jpwolfe9912/F051-ESC-4in1-V1/PNGs/3D_Back.png

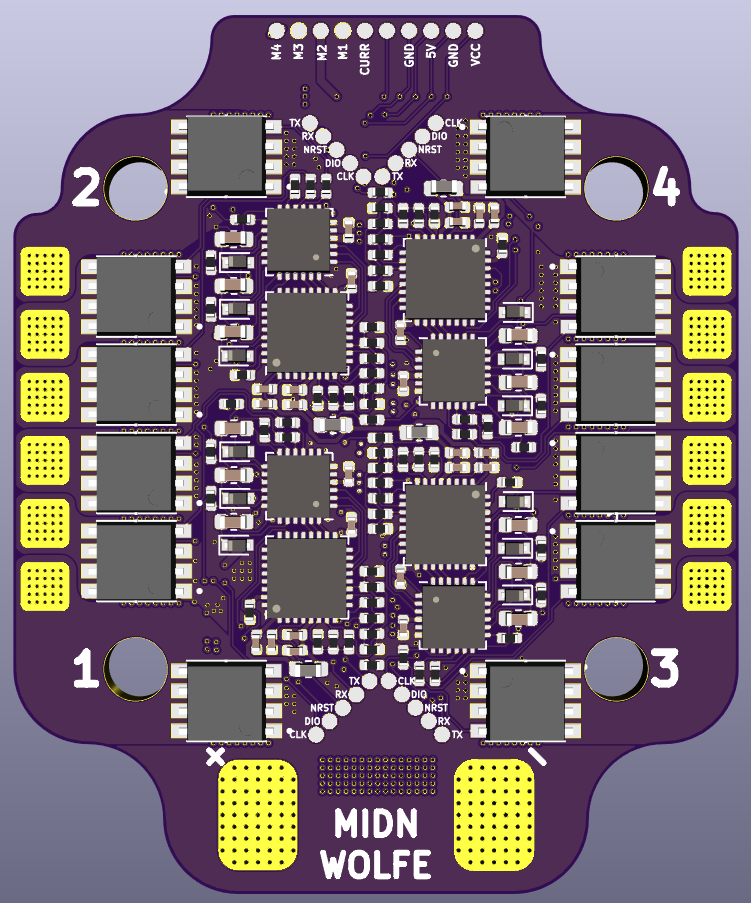
PNGs/3D_Back.png
