jpwolfe9912/F051-ESC-4in1-V1/PNGs/Design_In1Fill.png

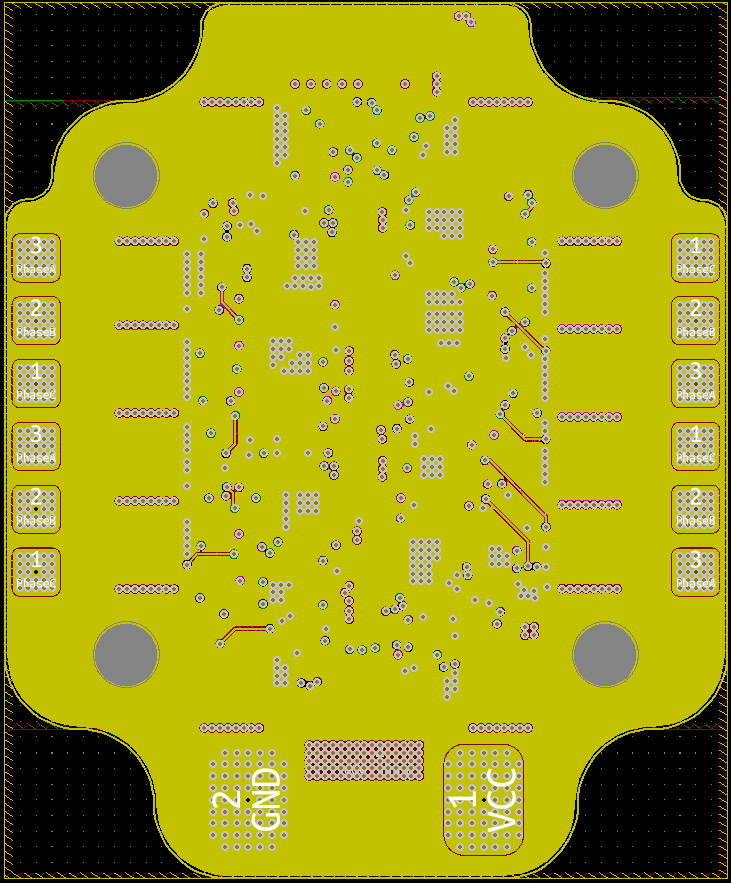
PNGs/Design_In1Fill.png
