jpwolfe9912/F051-ESC-4in1-V1/PNGs/Schematic_Main.png

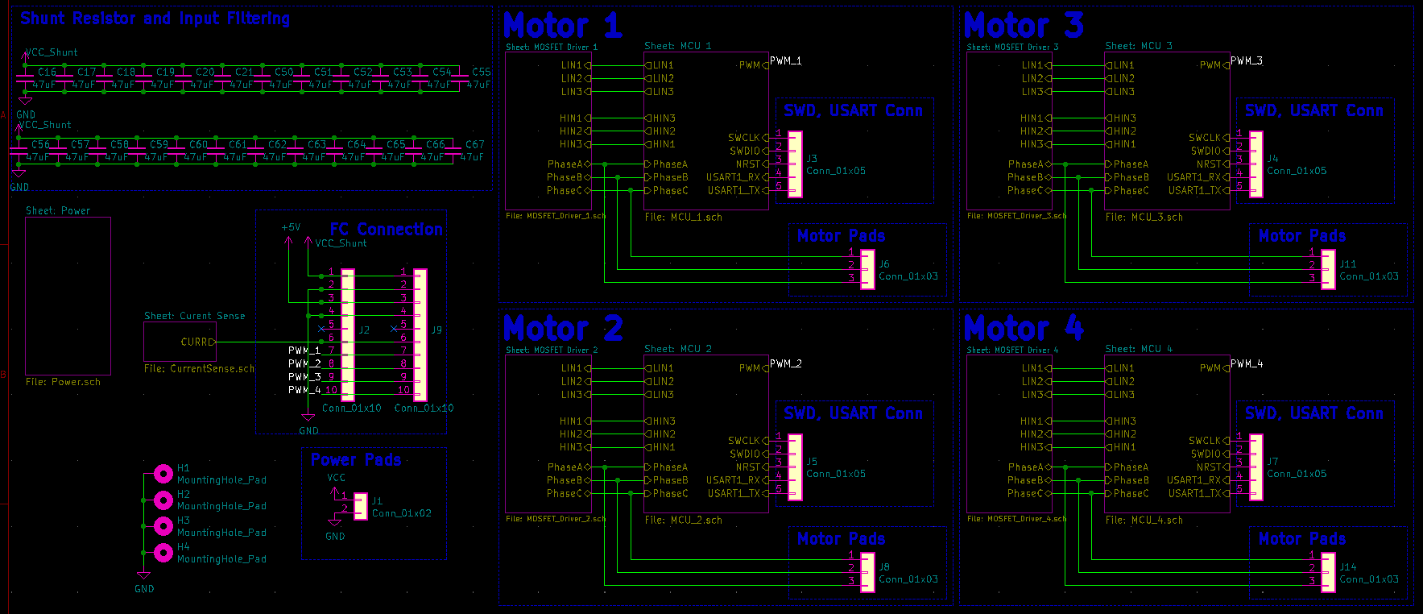
PNGs/Schematic_Main.png
