jpwolfe9912/F051-ESC-4in1-V1/PNGs/Schematic_MCU.png

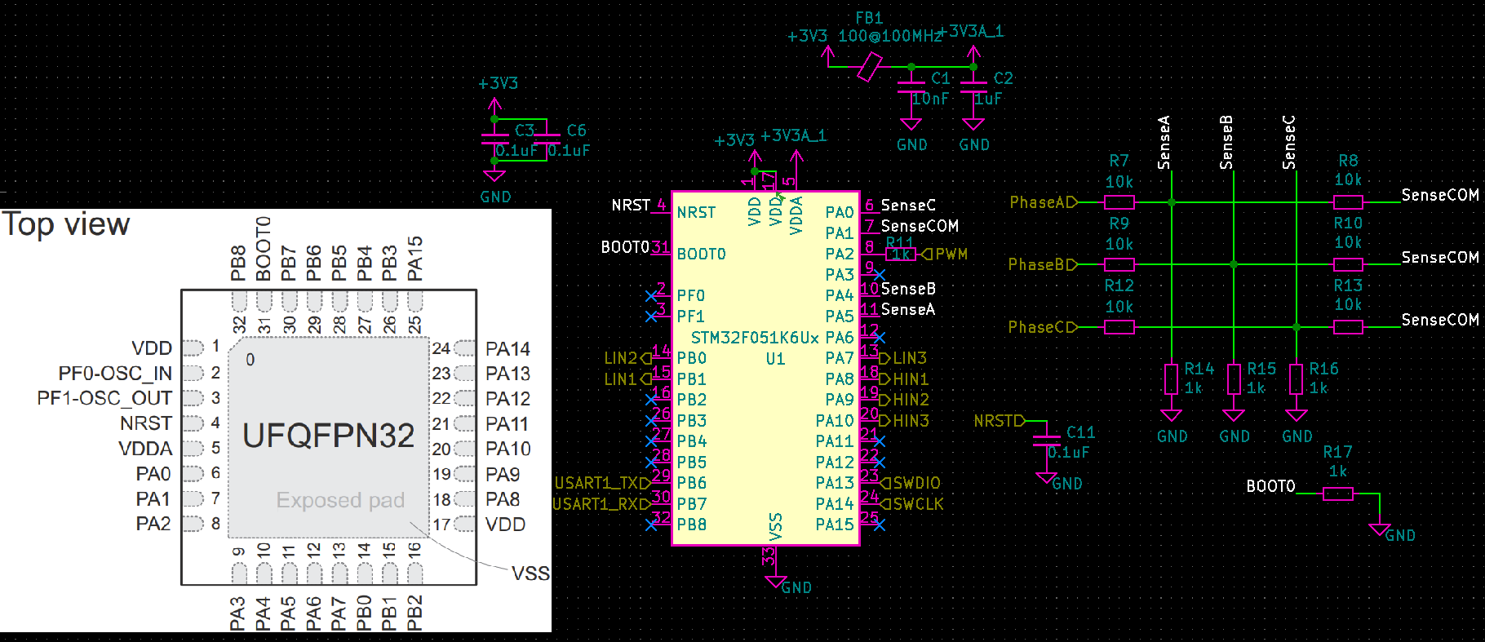
PNGs/Schematic_MCU.png
