jpwolfe9912/F051-ESC-4in1-V1/PNGs/STM32F051_Layout.png

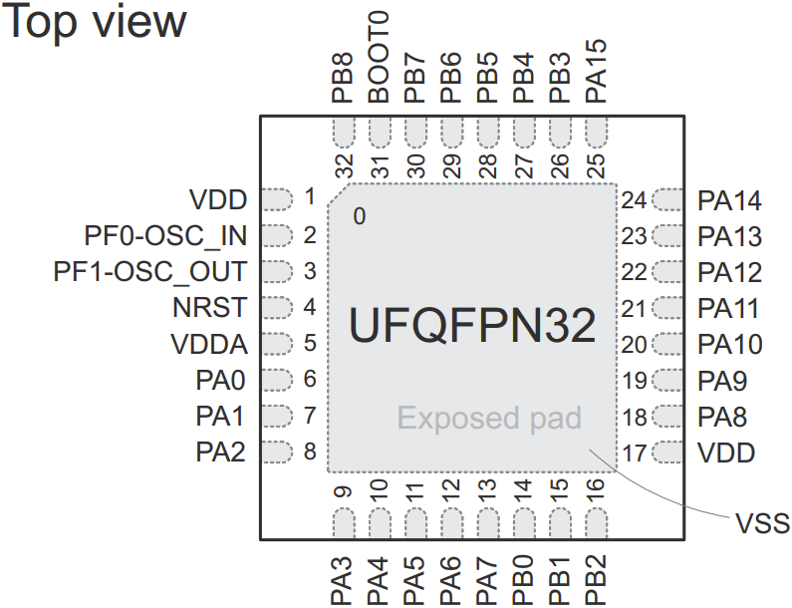
PNGs/STM32F051_Layout.png
