jpwolfe9912/F051-ESC-4in1-V1/PNGs/FD6288_Wiring.png

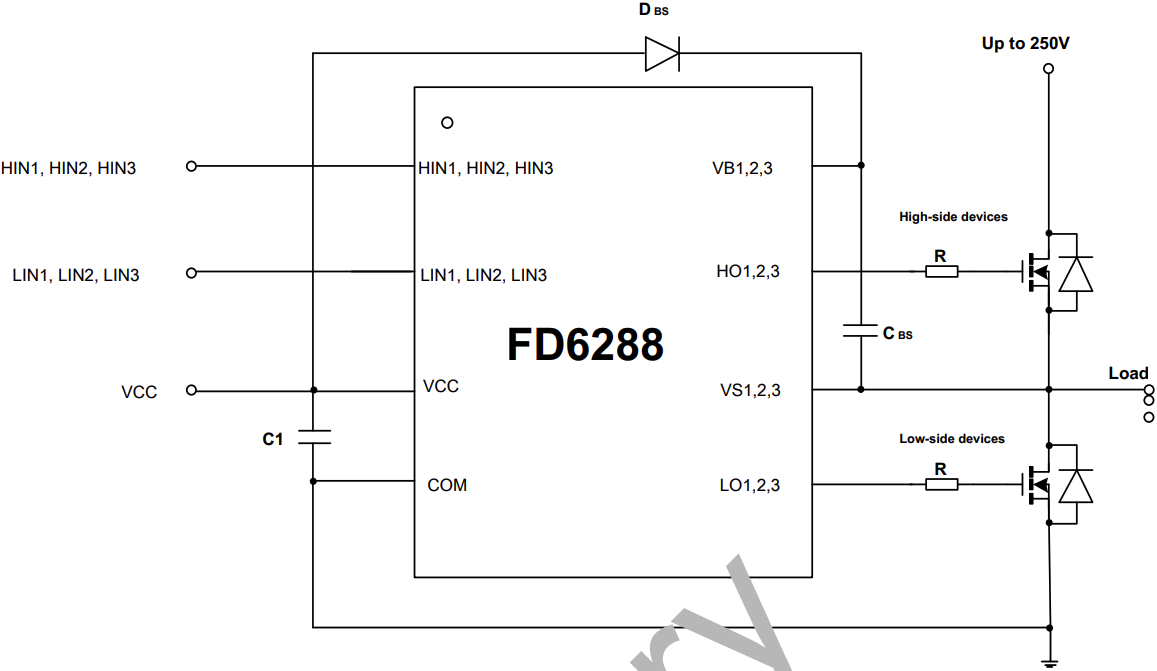
PNGs/FD6288_Wiring.png
